AndhikaFW/LuckFox-PicoMini-ParkingVision/camera-housing/Gemini_Generated_Image_xp5ablxp5ablxp5a.jpg

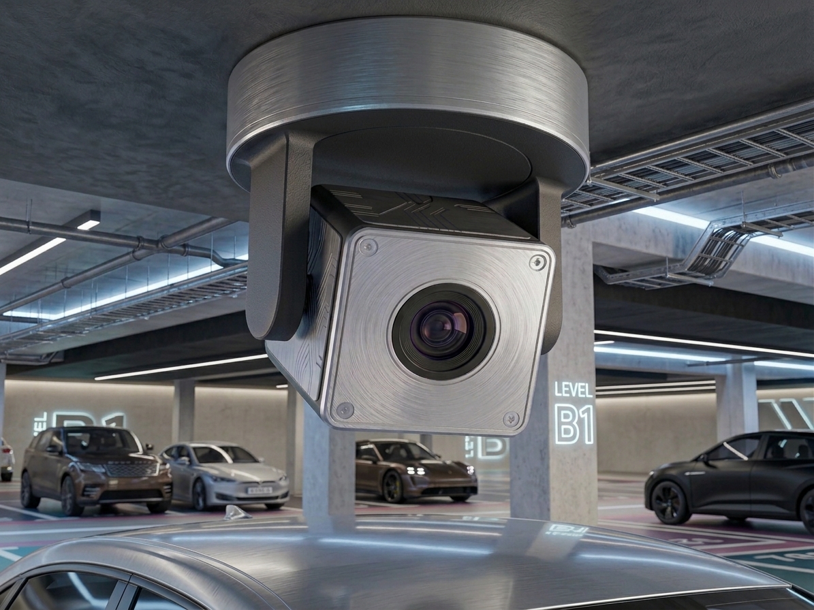
camera-housing/Gemini_Generated_Image_xp5ablxp5ablxp5a.jpg
