AndhikaFW/LuckFox-PicoMini-ParkingVision/camera-housing/casing_preview.png

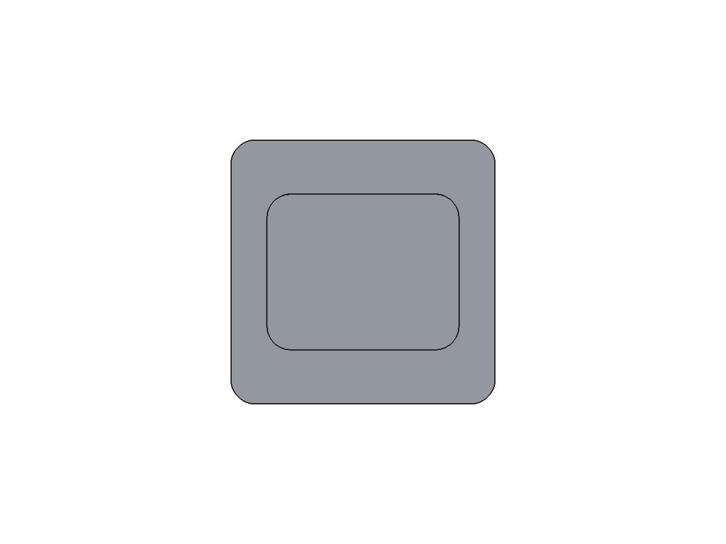
camera-housing/casing_preview.png
