AndhikaFW/LuckFox-PicoMini-ParkingVision/camera-housing/laser-cut/out/png/A1.png

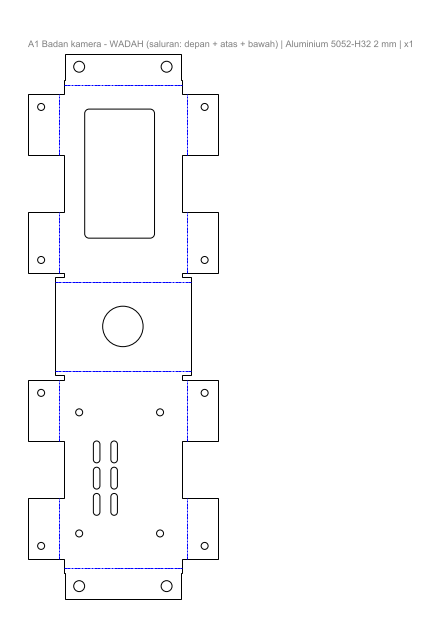
camera-housing/laser-cut/out/png/A1.png
