AndhikaFW/LuckFox-PicoMini-ParkingVision/camera-housing/laser-cut/out/png/A2.png

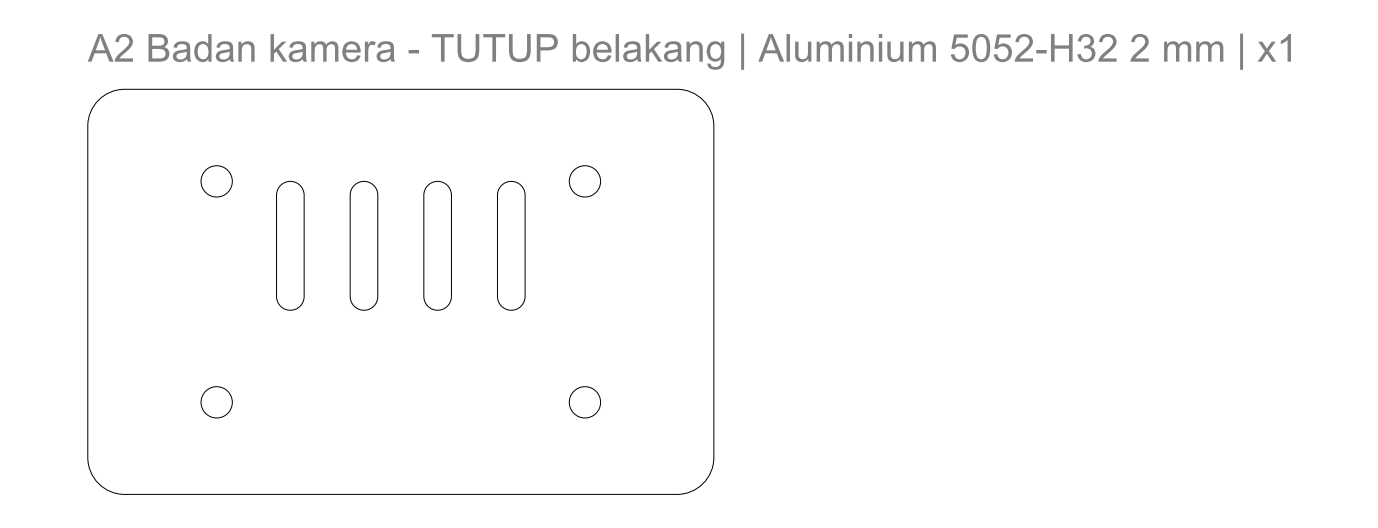
camera-housing/laser-cut/out/png/A2.png
