AndhikaFW/LuckFox-PicoMini-ParkingVision/camera-housing/laser-cut/out/png/B1.png

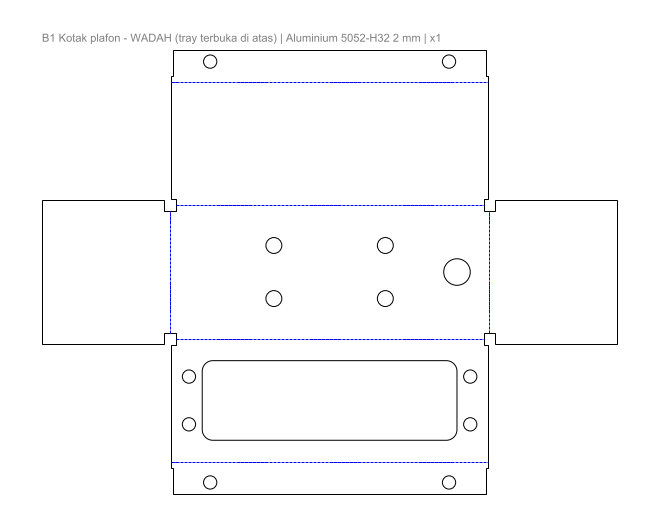
camera-housing/laser-cut/out/png/B1.png
