AndhikaFW/LuckFox-PicoMini-ParkingVision/camera-housing/laser-cut/out/png/B2.png

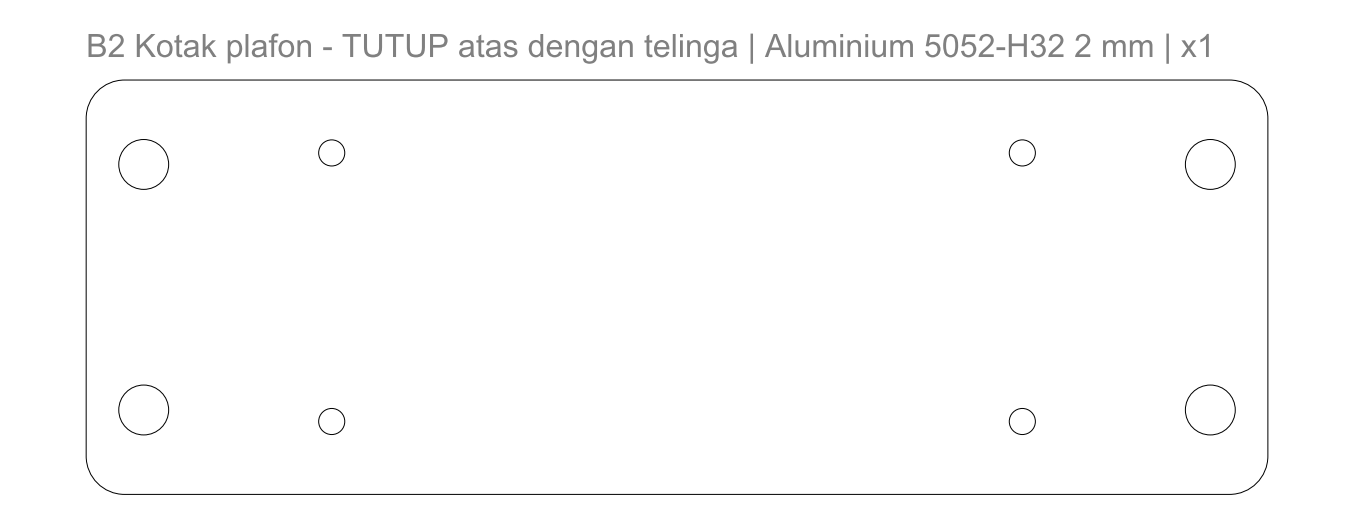
camera-housing/laser-cut/out/png/B2.png
