AndhikaFW/LuckFox-PicoMini-ParkingVision/camera-housing/laser-cut/out/png/S1.png

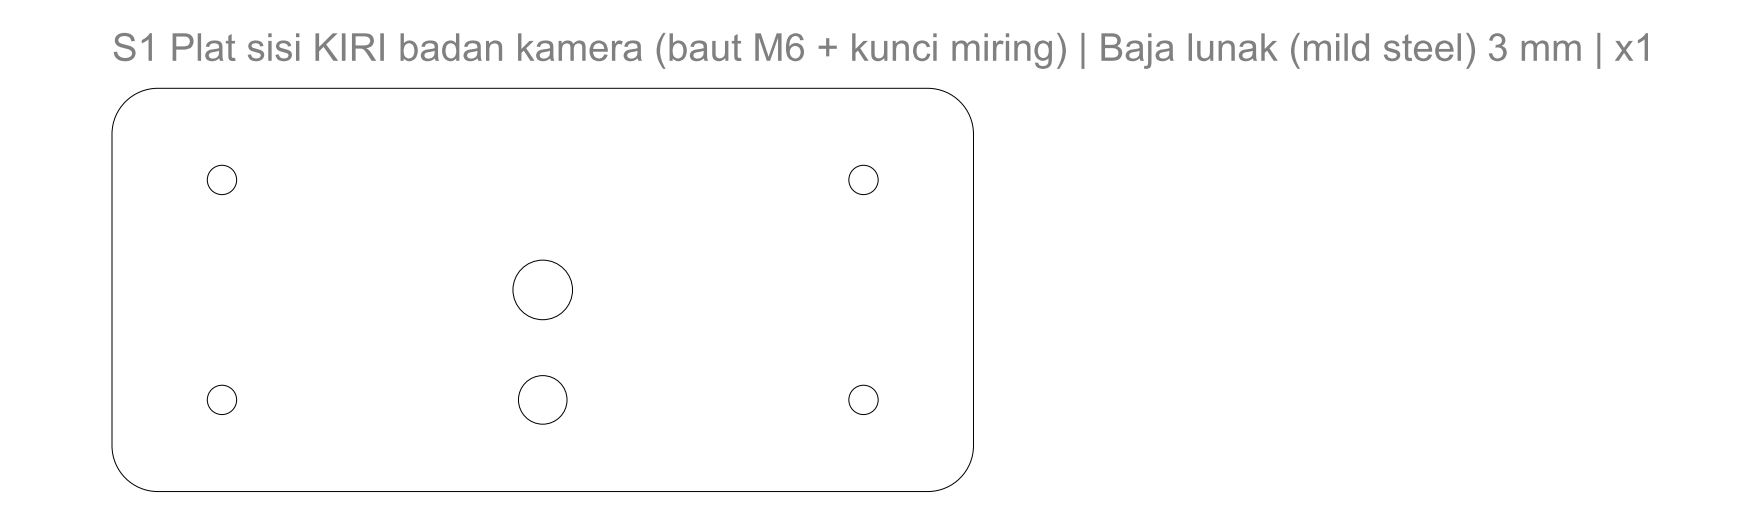
camera-housing/laser-cut/out/png/S1.png
