AndhikaFW/LuckFox-PicoMini-ParkingVision/camera-housing/laser-cut/out/png/S4.png

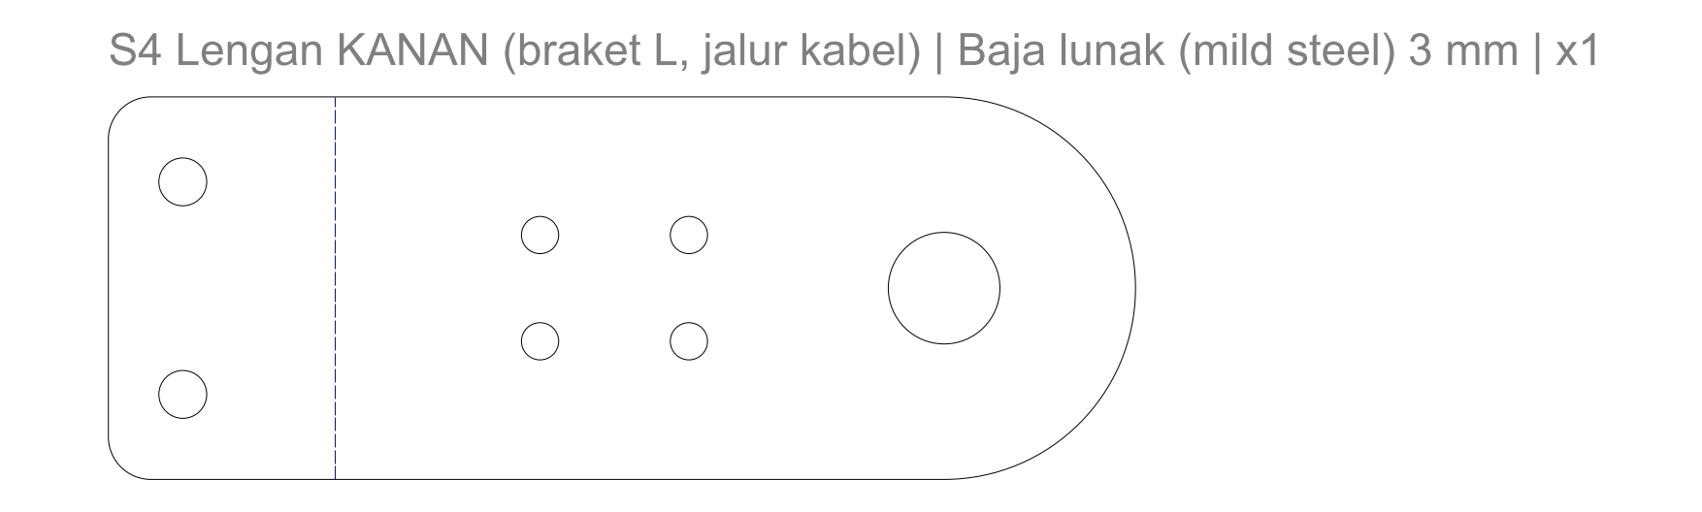
camera-housing/laser-cut/out/png/S4.png
