AndhikaFW/LuckFox-PicoMini-ParkingVision/camera-housing/laser-cut/out/png/sheet_aluminium_2mm.png

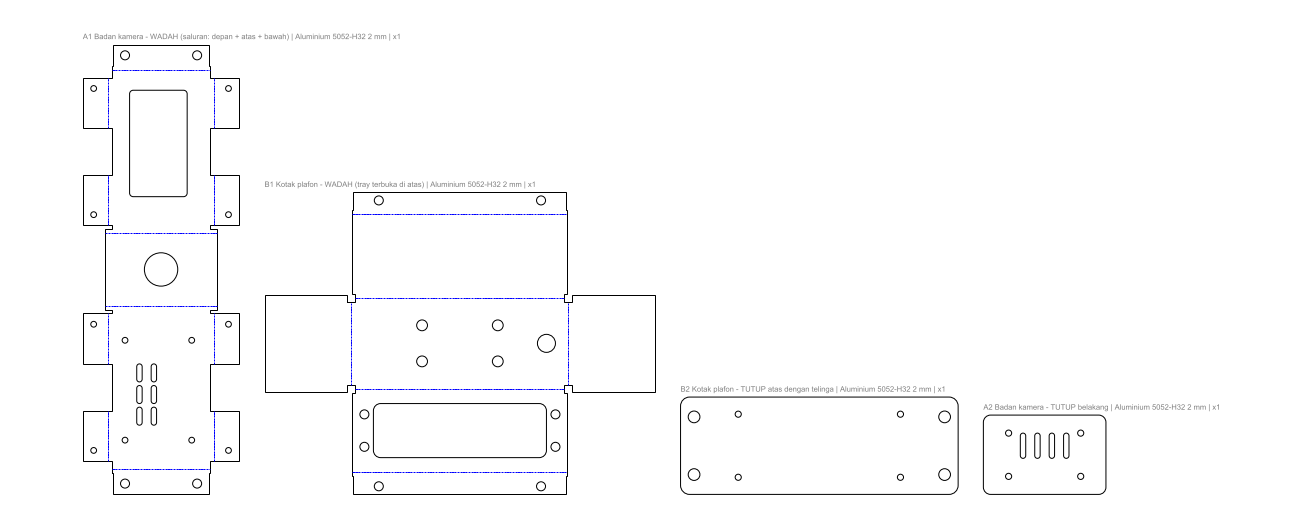
camera-housing/laser-cut/out/png/sheet_aluminium_2mm.png
