AndhikaFW/LuckFox-PicoMini-ParkingVision/camera-housing/laser-cut/out/dxf/S1_plat_sisi_kiri.dxf

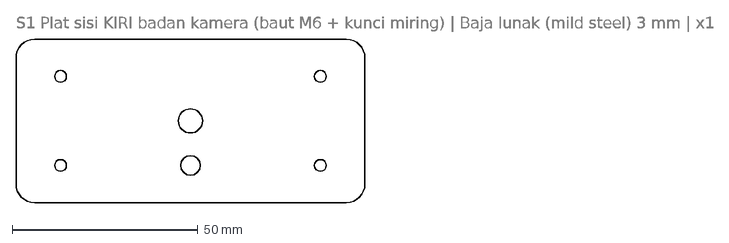
[picture p34: CAD file, 2026-10-07]
camera-housing/laser-cut/out/dxf/S1_plat_sisi_kiri.dxf
S1 Plat sisi KIRI badan kamera (baut M6 + kunci miring) | Baja lunak (mild steel) 3 mm | x1
