AndhikaFW/LuckFox-PicoMini-ParkingVision/camera-housing/laser-cut/out/dxf/A2_tutup_badan_kamera.dxf

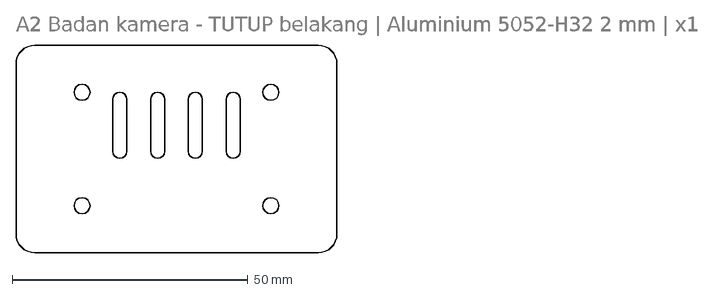
[picture p35: CAD file, 2026-10-07]
camera-housing/laser-cut/out/dxf/A2_tutup_badan_kamera.dxf
A2 Badan kamera - TUTUP belakang | Aluminium 5052-H32 2 mm | x1
