AndhikaFW/LuckFox-PicoMini-ParkingVision/camera-housing/ComponentBox.stl

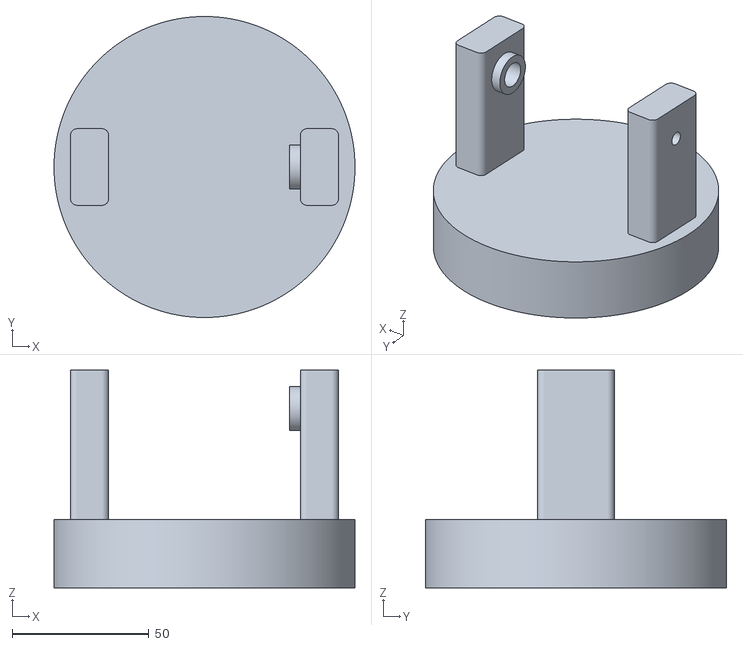
[picture p36: CAD file, 2026-10-07]
camera-housing/ComponentBox.stl
110.0 x 110.0 x 79.5
