AndhikaFW/LuckFox-PicoMini-ParkingVision/camera-housing/laser-cut/out/dxf/S3_lengan_kiri_slot.dxf

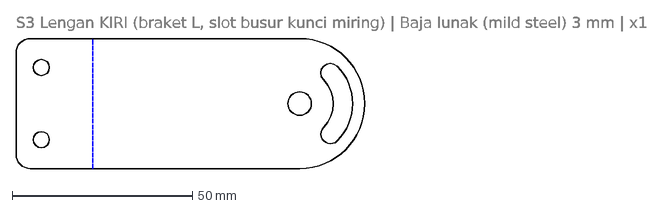
[picture p37: CAD file, 2026-10-07]
camera-housing/laser-cut/out/dxf/S3_lengan_kiri_slot.dxf
S3 Lengan KIRI (braket L, slot busur kunci miring) | Baja lunak (mild steel) 3 mm | x1
