AndhikaFW/LuckFox-PicoMini-ParkingVision/camera-housing/laser-cut/out/dxf/A3_tutup_jendela_RF_akrilik.dxf

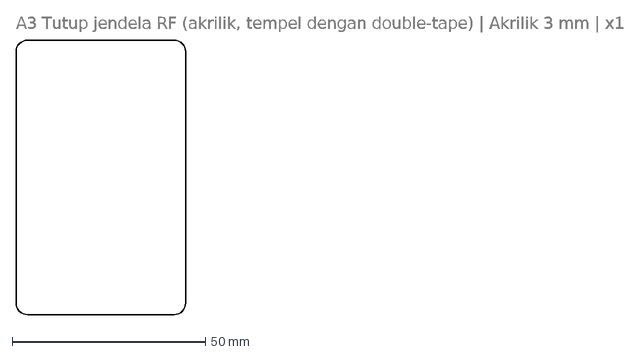
[picture p38: CAD file, 2026-10-07]
camera-housing/laser-cut/out/dxf/A3_tutup_jendela_RF_akrilik.dxf
A3 Tutup jendela RF (akrilik, tempel dengan double-tape) | Akrilik 3 mm | x1
