AndhikaFW/LuckFox-PicoMini-ParkingVision/camera-housing/laser-cut/out/dxf/S4_lengan_kanan_kabel.dxf

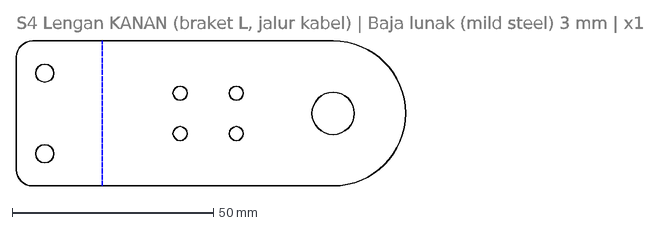
[picture p39: CAD file, 2026-10-07]
camera-housing/laser-cut/out/dxf/S4_lengan_kanan_kabel.dxf
S4 Lengan KANAN (braket L, jalur kabel) | Baja lunak (mild steel) 3 mm | x1
