AndhikaFW/LuckFox-PicoMini-ParkingVision/camera-housing/assembly_preview.png

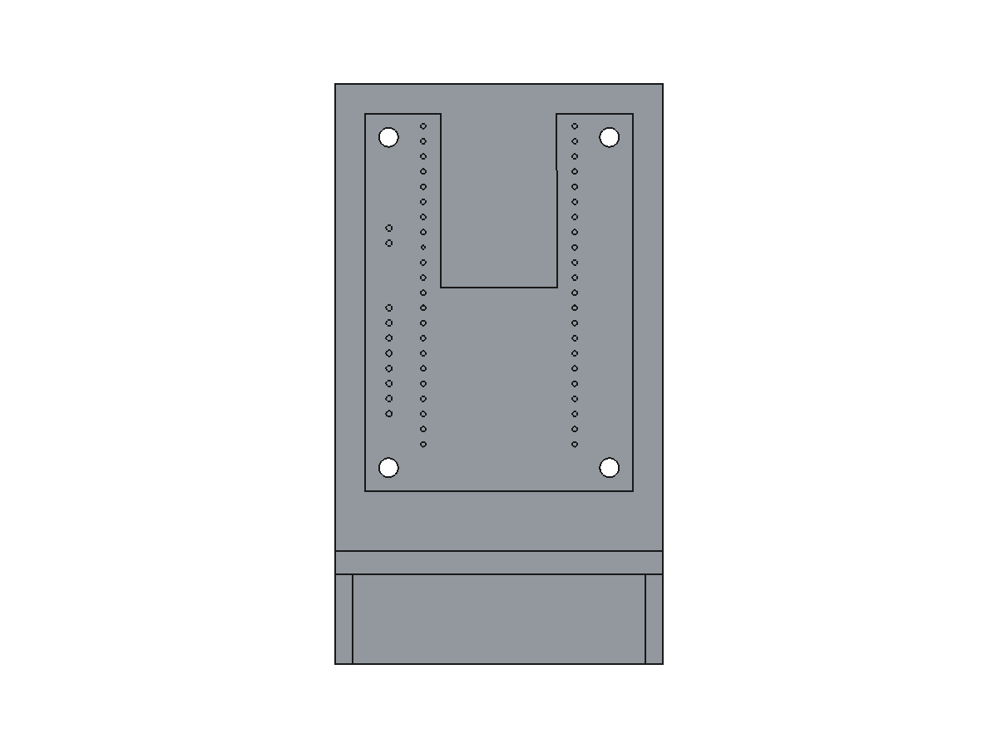
camera-housing/assembly_preview.png
