AndhikaFW/LuckFox-PicoMini-ParkingVision/camera-housing/full_assembly_preview.png

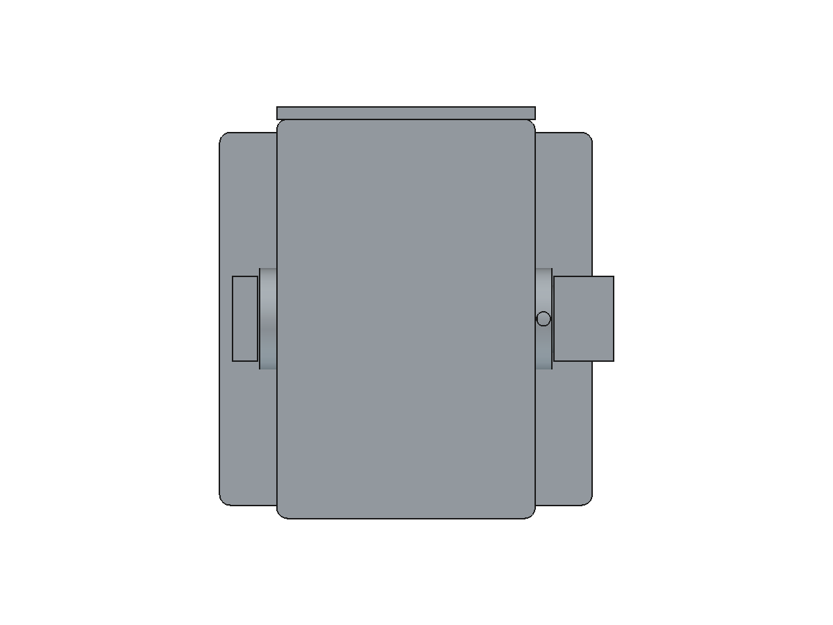
camera-housing/full_assembly_preview.png
