AndhikaFW/LuckFox-PicoMini-ParkingVision/camera-housing/laser-cut/out/assembly.png

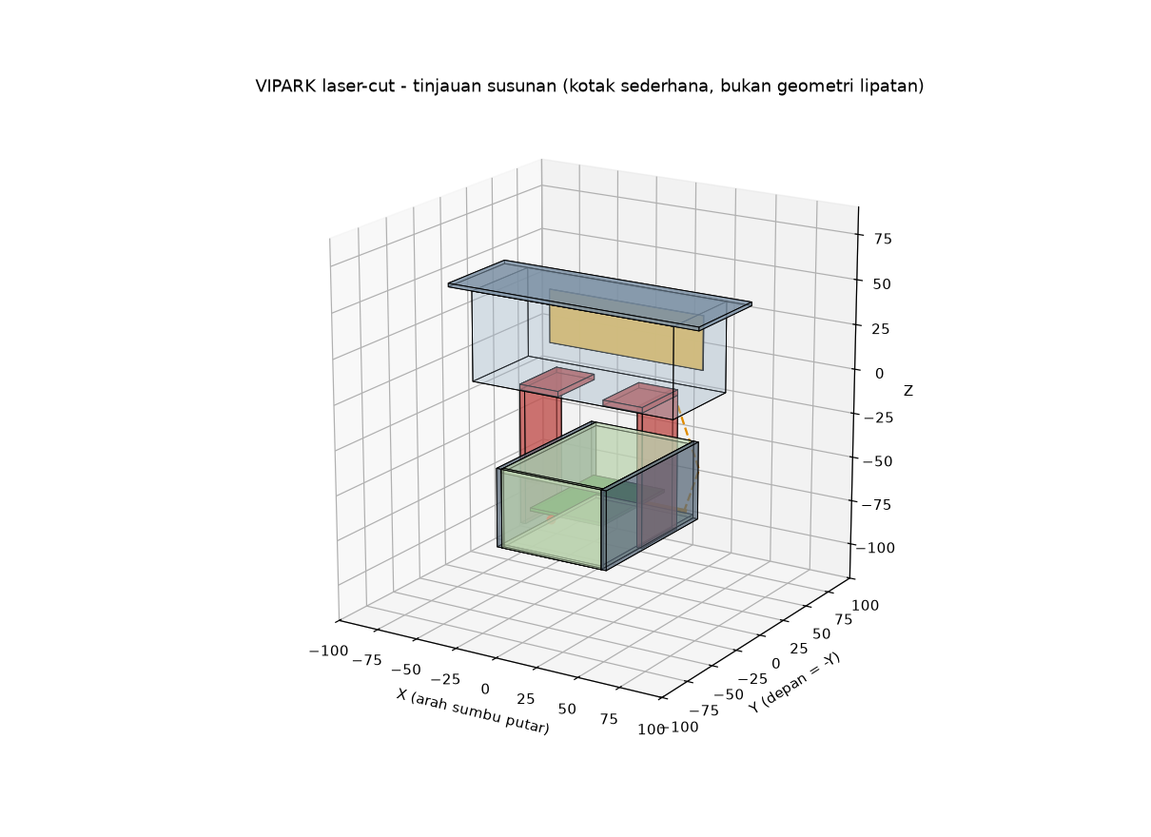
camera-housing/laser-cut/out/assembly.png
