AndhikaFW/LuckFox-PicoMini-ParkingVision/LuckFox-RAP-Shield-PCB/wiring_diagram.png

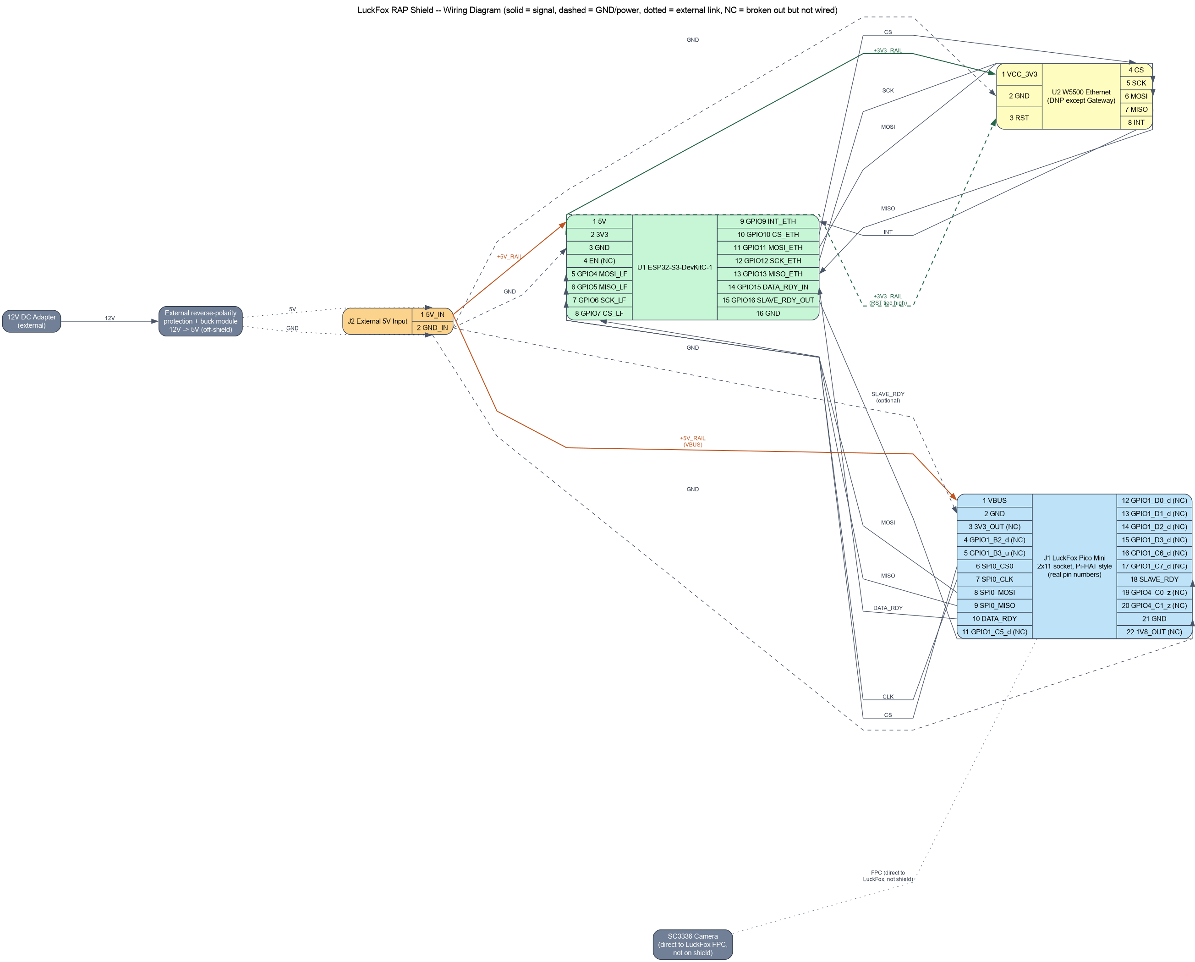
LuckFox-RAP-Shield-PCB/wiring_diagram.png
